dmitryshagin/dynamic_blender/firmware/spi.c

/***************************************************************************//**
 *   @file   Communication.c
 *   @brief  Implementation of Communication Driver.
 *   @author DBogdan (dragos.bogdan@analog.com)
********************************************************************************
 * Copyright 2012(c) Analog Devices, Inc.
 *
 * All rights reserved.
 *
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
********************************************************************************
 *   SVN Revision: 500
*******************************************************************************/

/******************************************************************************/
/* Include Files                                                              */
/******************************************************************************/
#include "spi.h"
#include <avr/io.h>

/***************************************************************************//**
 * @brief Initializes the SPI communication peripheral.
 *
 * @param lsbFirst - Transfer format (0 or 1).
 *                   Example: 0x0 - MSB first.
 *                            0x1 - LSB first.
 * @param clockFreq - SPI clock frequency (Hz).
 *                    Example: 1000 - SPI clock frequency is 1 kHz.
 * @param clockPol - SPI clock polarity (0 or 1).
 *                   Example: 0x0 - idle state for SPI clock is low.
 *	                          0x1 - idle state for SPI clock is high.
 * @param clockPha - SPI clock phase (0 or 1).
 *                   Example: 0x0 - data is latched on the leading edge of SPI
 *                                  clock and data changes on trailing edge.
 *                            0x1 - data is latched on the trailing edge of SPI
 *                                  clock and data changes on the leading edge.
 *
 * @return 0 - Initialization failed, 1 - Initialization succeeded.
*******************************************************************************/
unsigned char SPI_Init(unsigned char lsbFirst,
                       unsigned long clockFreq,
                       unsigned char clockPol,
                       unsigned char clockPha)
{
	DDR_SPI &= ~((1<<DD_MOSI)|(1<<DD_MISO)|(1<<DD_SS)|(1<<DD_SCK));
    // Define the following pins as output
    DDR_SPI |= ((1<<DD_MOSI)|(1<<DD_SS)|(1<<DD_SCK));
   

	SPCR = ((1<<SPE)|               // SPI Enable
            (0<<SPIE)|              // SPI Interupt Disable
            (lsbFirst<<DORD)|       // Data Order (0:MSB first / 1:LSB first)
            (1<<MSTR)|              // Master/Slave select   
            (0<<SPR1)|(1<<SPR0)|    // SPI Clock Rate
            (clockPol<<CPOL)|       // Clock Polarity (0:SCK low / 1:SCK hi when idle)
            (clockPha<<CPHA));      // Clock Phase (0:leading / 1:trailing edge sampling)


	
    return(1);
}


/***************************************************************************//**
 * @brief Writes data to SPI.
 *
 * @param data - Write data buffer:
 *               - first byte is the chip select number;
 *               - from the second byte onwards are located data bytes to write.
 * @param bytesNumber - Number of bytes to write.
 *
 * @return Number of written bytes.
*******************************************************************************/
unsigned char SPI_Write(unsigned char* data,
                        unsigned char bytesNumber)
{
    unsigned char chipSelect    = data[0];
    unsigned char writeData[4]  = {0, 0, 0, 0};
    // unsigned char readData[4]   = {0, 0, 0, 0};
    unsigned char i          = 0;
    
    for(i = 0;i < bytesNumber;i ++)
    {
        writeData[i] = data[i + 1];
    }
    if(chipSelect == 1)
    {
        ADI_PART_CS_LOW;
    }
    
    for(i = 0;i < bytesNumber;i ++)
    {
        SPDR = (uint8_t)writeData[i];
        while((SPSR & (1<<SPIF))==0);
        // readData[i] = SPDR; 
    }
    if(chipSelect == 1)
    {
        ADI_PART_CS_HIGH;
    }

    return(bytesNumber);
}

/***************************************************************************//**
 * @brief Reads data from SPI.
 *
 * @param data - As an input parameter, data represents the write buffer:
 *               - first byte is the chip select number;
 *               - from the second byte onwards are located data bytes to write.
 *               As an output parameter, data represents the read buffer:
 *               - from the first byte onwards are located the read data bytes. 
 * @param bytesNumber - Number of bytes to write.
 *
 * @return Number of written bytes.
*******************************************************************************/
unsigned char SPI_Read(unsigned char* data,
                       unsigned char bytesNumber)
{
    unsigned char chipSelect    = data[0];
    unsigned char writeData[4]  = {0, 0, 0, 0};
    unsigned char readData[4]   = {0, 0, 0, 0};
    unsigned char i          = 0;
    
    for(i = 0;i < bytesNumber;i ++)
    {
        writeData[i] = data[i + 1];
    }
    if(chipSelect == 1)
    {
        ADI_PART_CS_LOW;
    }
    
    for(i = 0;i < bytesNumber;i ++)
    {
        SPDR = (uint8_t)writeData[i];
        while((SPSR & (1<<SPIF))==0);
        readData[i] = SPDR;    }
    if(chipSelect == 1)
    {
        ADI_PART_CS_HIGH;
    }

    for(i = 0;i < bytesNumber;i ++)
    {
        data[i] = readData[i];
    }

    return(bytesNumber);



 //    ADI_PART_CS_LOW;
	// uint8_t i;      

 //    for (i = 1; i < bytesNumber+1; i++) {
 //        SPDR = 0x00;
 //        while((SPSR & (1<<SPIF))==0);
 //        data[i] = SPDR;
 //    }
 //    ADI_PART_CS_HIGH;
	// return(bytesNumber);
}
